richardhawthorn/Build/images/DSC_7647.JPG

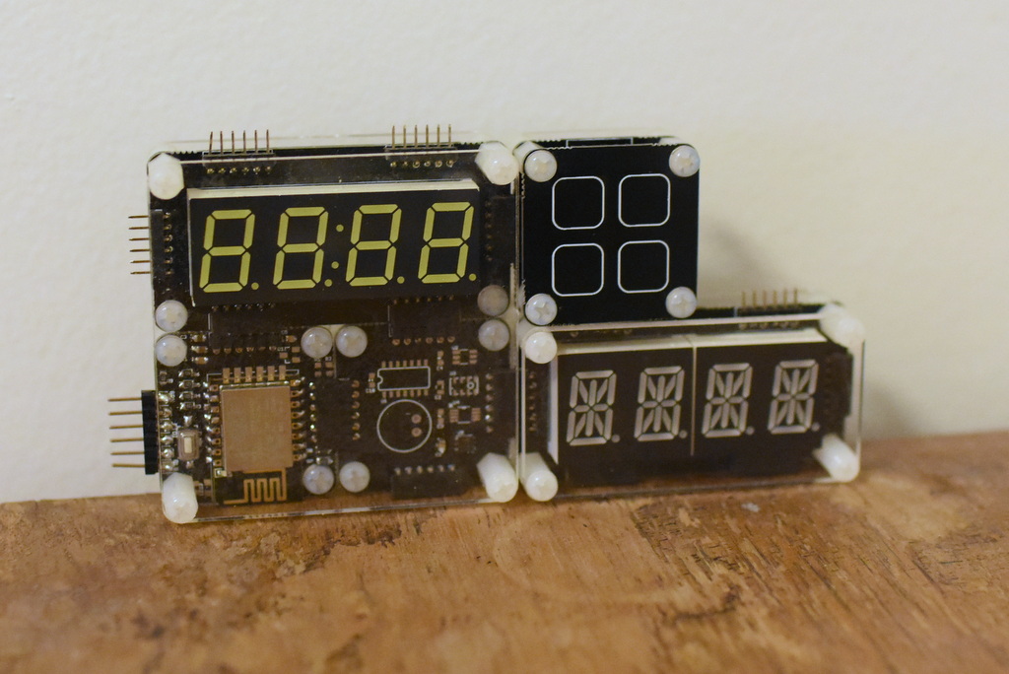
images/DSC_7647.JPG
