richardhawthorn/Build/Boards/7 Segment/images/pcb_back.png

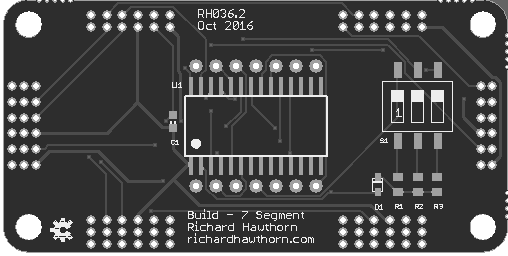
Boards/7 Segment/images/pcb_back.png
