richardhawthorn/Build/Boards/14 Segment/images/DSC_7678.JPG

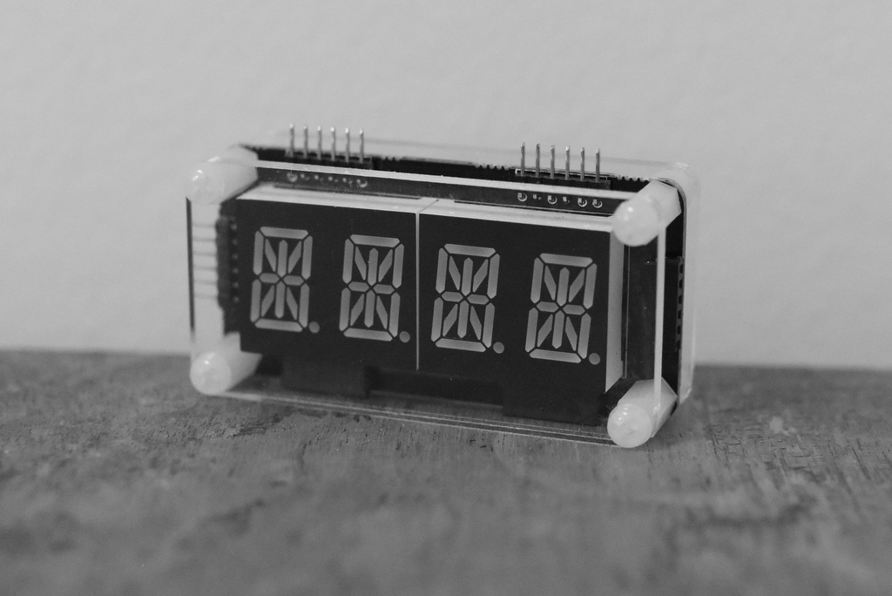
Boards/14 Segment/images/DSC_7678.JPG
