richardhawthorn/Build/Boards/Buttons/images/pcb_back.png

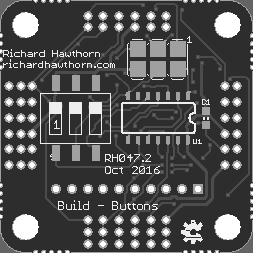
Boards/Buttons/images/pcb_back.png
