richardhawthorn/Build/Boards/Buttons/images/pcb_back_btn.png

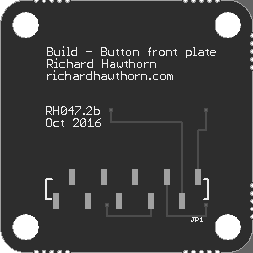
Boards/Buttons/images/pcb_back_btn.png
