richardhawthorn/Build/Boards/Buttons/images/pcb_front.png

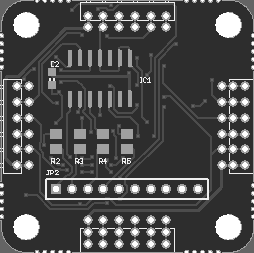
Boards/Buttons/images/pcb_front.png
