richardhawthorn/Build/Boards/Buttons/images/pcb_front_btn.png

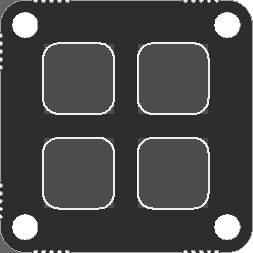
Boards/Buttons/images/pcb_front_btn.png
