richardhawthorn/Build/Boards/Dial/images/pcb_back.png

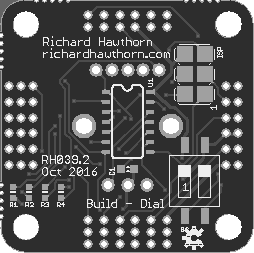
Boards/Dial/images/pcb_back.png
