richardhawthorn/Build/Boards/Dial/images/pcb_front.png

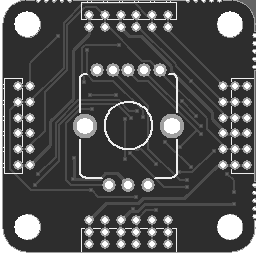
Boards/Dial/images/pcb_front.png
