richardhawthorn/Build/Boards/External Sensors/images/pcb_back.png

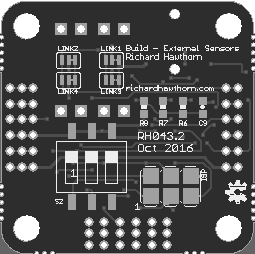
Boards/External Sensors/images/pcb_back.png
