richardhawthorn/Build/Boards/External Sensors/images/pcb_front.png

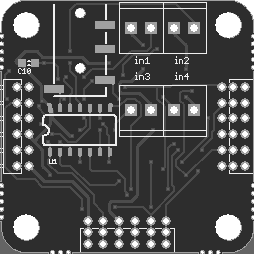
Boards/External Sensors/images/pcb_front.png
