richardhawthorn/Build/Boards/Mini 8x8 Matrix/images/pcb_back.png

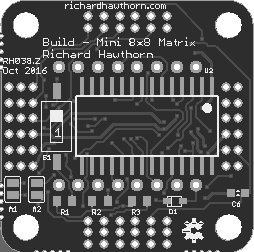
Boards/Mini 8x8 Matrix/images/pcb_back.png
