richardhawthorn/Build/Boards/Mini 8x8 Matrix/images/pcb_front.png

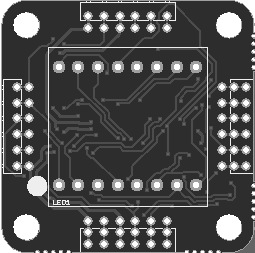
Boards/Mini 8x8 Matrix/images/pcb_front.png
