richardhawthorn/Build/Boards/Neopixel/images/pcb_back.png

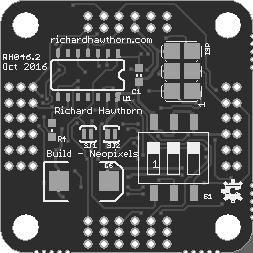
Boards/Neopixel/images/pcb_back.png
