richardhawthorn/Build/Boards/Neopixel/images/pcb_front.png

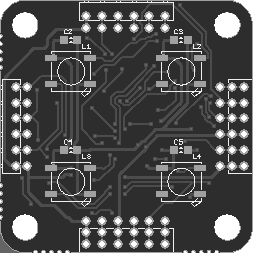
Boards/Neopixel/images/pcb_front.png
