richardhawthorn/Build/Boards/Proto i2c/images/pcb_back.png

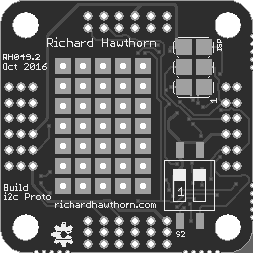
Boards/Proto i2c/images/pcb_back.png
