richardhawthorn/Build/Boards/Proto i2c/images/pcb_front.png

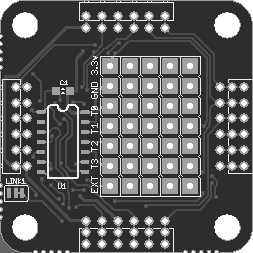
Boards/Proto i2c/images/pcb_front.png
