richardhawthorn/Build/Boards/Proto/images/pcb_back.png

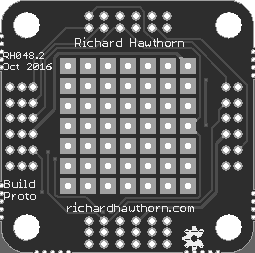
Boards/Proto/images/pcb_back.png
