richardhawthorn/Build/Boards/Proto/images/pcb_front.png

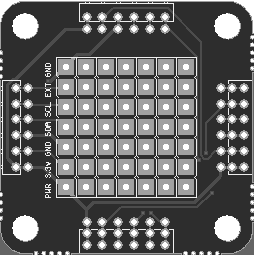
Boards/Proto/images/pcb_front.png
