richardhawthorn/Build/Boards/Relay/images/pcb_back.png

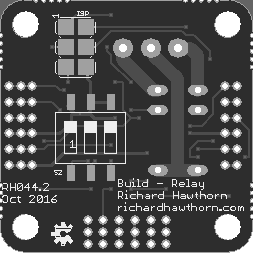
Boards/Relay/images/pcb_back.png
