richardhawthorn/Build/Boards/RF:BLE/images/pcb_back.png

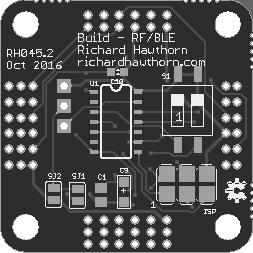
Boards/RF:BLE/images/pcb_back.png
