richardhawthorn/Build/Boards/RF:BLE/images/pcb_front.png

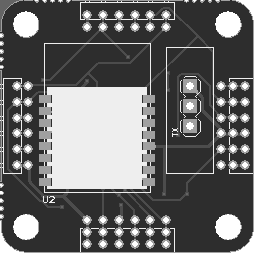
Boards/RF:BLE/images/pcb_front.png
