richardhawthorn/Build/Boards/Sensors/images/pcb_back.png

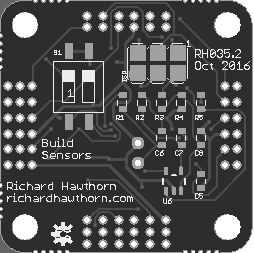
Boards/Sensors/images/pcb_back.png
