richardhawthorn/Build/Boards/Sensors/images/pcb_front.png

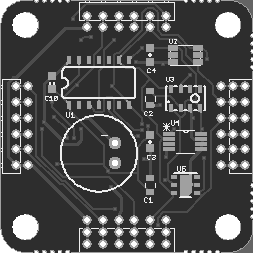
Boards/Sensors/images/pcb_front.png
