richardhawthorn/Build/Boards/Slider/images/pcb_back.png

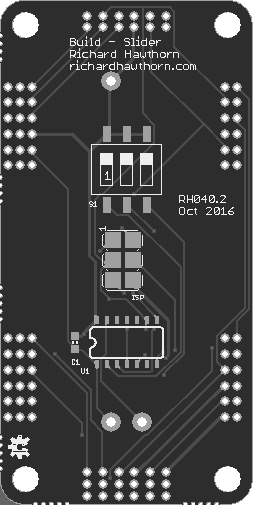
Boards/Slider/images/pcb_back.png
