richardhawthorn/Build/Boards/Wifi Base/images/pcb_back.png

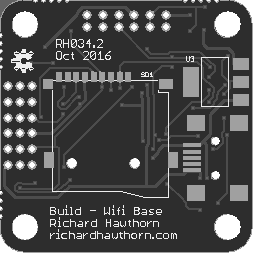
Boards/Wifi Base/images/pcb_back.png
