richardhawthorn/Build/Boards/Wifi Base/images/pcb_front.png

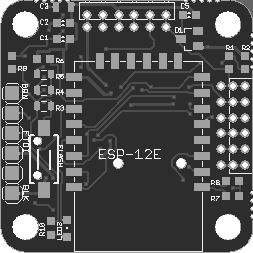
Boards/Wifi Base/images/pcb_front.png
