richardhawthorn/Build/images/DSC_7637.JPG

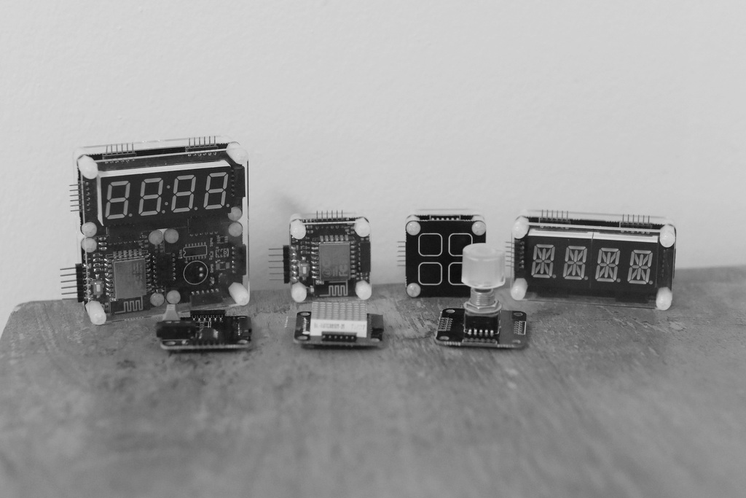
images/DSC_7637.JPG
