richardhawthorn/Build/Boards/RF:BLE/pcb/RH045.2/RH045.2.brd

## EAGLE design Boards/RF:BLE/pcb/RH045.2/RH045.2.brd (2018-01-28)

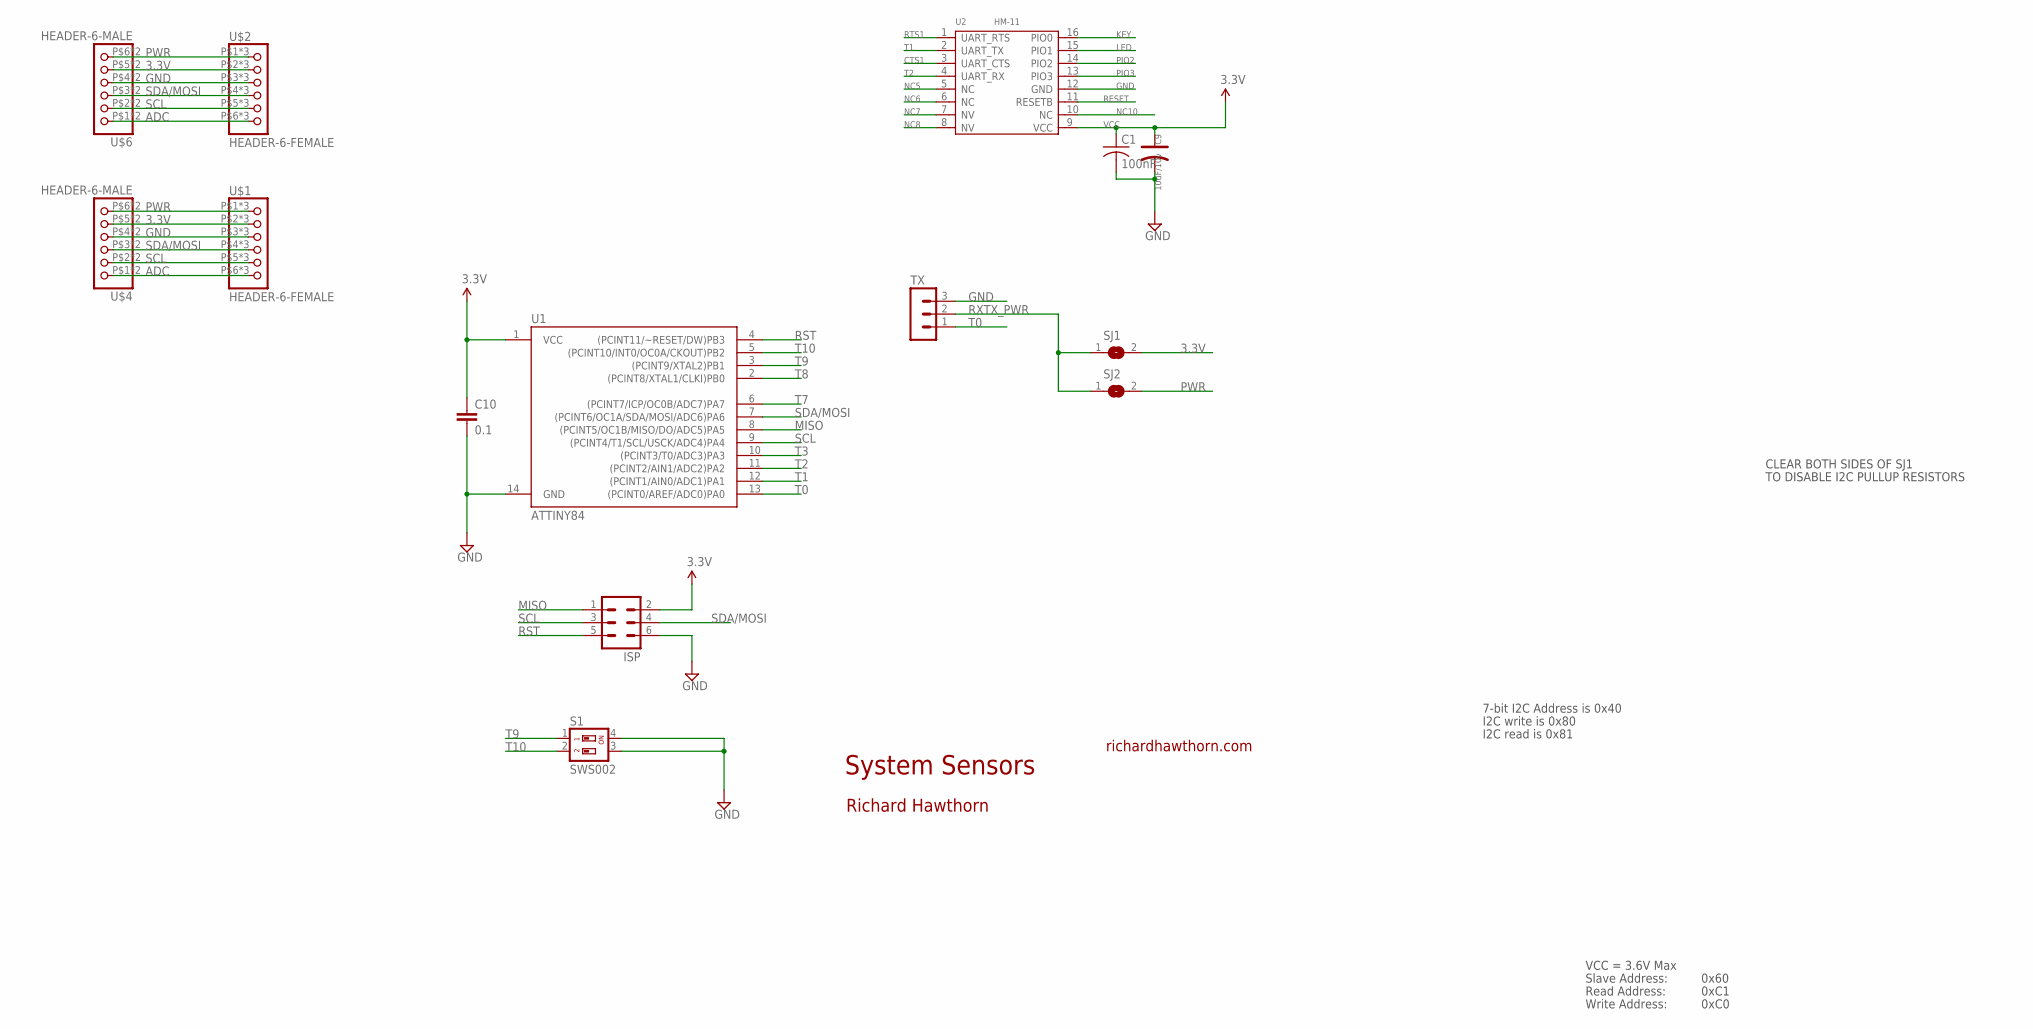
[picture p61: schematic RH045.2.sch]

Parts:
C1: 100nF; C0805
C9: 10uF/10v; AVX-A
C10: 0.1; 0603-CAP
ISP: MA03-2
S1: SWS002; SMS-002
SJ1, SJ2: SJ
TX: MA03-1
U1: ATTINY84; SO14
U2: HM-11; 16P-18.5X13.5X0.8
U$1, U$2: HEADER-6-FEMALE; 2MMHEADER6
U$4, U$6: HEADER-6-MALE; 2MMHEADERPIN6

Connections:
3.3V: C10.1, ISP.2, SJ1.2, U1.1 (VCC), U$1.P$2 (2), U$1.P$10 (2), U$1.P$18 (2), U$2.P$2 (2), U$2.P$10 (2), U$2.P$18 (2), U$4.P$5 (5), U$4.P$13 (5), U$6.P$5 (5), U$6.P$13 (5)
ADC: U$1.P$6 (6), U$1.P$14 (6), U$1.P$22 (6), U$2.P$6 (6), U$2.P$14 (6), U$2.P$22 (6), U$4.P$1 (1), U$4.P$9 (1), U$6.P$1 (1), U$6.P$9 (1)
CTS1: U2.3 (UART_CTS)
GND: C1.2, C9.-, C10.2, ISP.6, S1.3, S1.4, TX.3, U1.14 (GND), U2.12 (GND), U$1.P$3 (3), U$1.P$11 (3), U$1.P$19 (3), U$2.P$3 (3), U$2.P$11 (3), U$2.P$19 (3), U$4.P$4 (4), U$4.P$12 (4), U$6.P$4 (4), U$6.P$12 (4)
KEY: U2.16 (PIO0)
LED: U2.15 (PIO1)
MISO: ISP.1, U1.8 ((PCINT5/OC1B/MISO/DO/ADC5)PA5)
NC5: U2.5 (NC)
NC6: U2.6 (NC)
NC7: U2.7 (NV)
NC8: U2.8 (NV)
NC10: U2.10 (NC)
PIO2: U2.14 (PIO2)
PIO3: U2.13 (PIO3)
PWR: SJ2.2, U$1.P$1 (1), U$1.P$9 (1), U$1.P$17 (1), U$2.P$1 (1), U$2.P$9 (1), U$2.P$17 (1), U$4.P$6 (6), U$4.P$14 (6), U$6.P$6 (6), U$6.P$14 (6)
RESET: U2.11 (RESETB)
RST: ISP.5, U1.4 ((PCINT11/~RESET/DW)PB3)
RTS1: U2.1 (UART_RTS)
RXTX_PWR: SJ1.1, SJ2.1, TX.2
SCL: ISP.3, U1.9 ((PCINT4/T1/SCL/USCK/ADC4)PA4), U$1.P$5 (5), U$1.P$13 (5), U$1.P$21 (5), U$2.P$5 (5), U$2.P$13 (5), U$2.P$21 (5), U$4.P$2 (2), U$4.P$10 (2), U$6.P$2 (2), U$6.P$10 (2)
SDA/MOSI: ISP.4, U1.7 ((PCINT6/OC1A/SDA/MOSI/ADC6)PA6), U$1.P$4 (4), U$1.P$12 (4), U$1.P$20 (4), U$2.P$4 (4), U$2.P$12 (4), U$2.P$20 (4), U$4.P$3 (3), U$4.P$11 (3), U$6.P$3 (3), U$6.P$11 (3)
T0: TX.1, U1.13 ((PCINT0/AREF/ADC0)PA0)
T1: U1.12 ((PCINT1/AIN0/ADC1)PA1), U2.2 (UART_TX)
T2: U1.11 ((PCINT2/AIN1/ADC2)PA2), U2.4 (UART_RX)
T3: U1.10 ((PCINT3/T0/ADC3)PA3)
T7: U1.6 ((PCINT7/ICP/OC0B/ADC7)PA7)
T8: U1.2 ((PCINT8/XTAL1/CLKI)PB0)
T9: S1.1, U1.3 ((PCINT9/XTAL2)PB1)
T10: S1.2, U1.5 ((PCINT10/INT0/OC0A/CKOUT)PB2)
VCC: C1.1, C9.+, U2.9 (VCC)

Notes on the sheet:
System Sensors
richardhawthorn.com
Richard Hawthorn
CLEAR BOTH SIDES OF SJ1
TO DISABLE I2C PULLUP RESISTORS
7-bit I2C Address is 0x40
I2C write is 0x80
I2C read is 0x81
VCC = 3.6V Max
Read Address:
Write Address:
Slave Address:
0x60
0xC1
0xC0

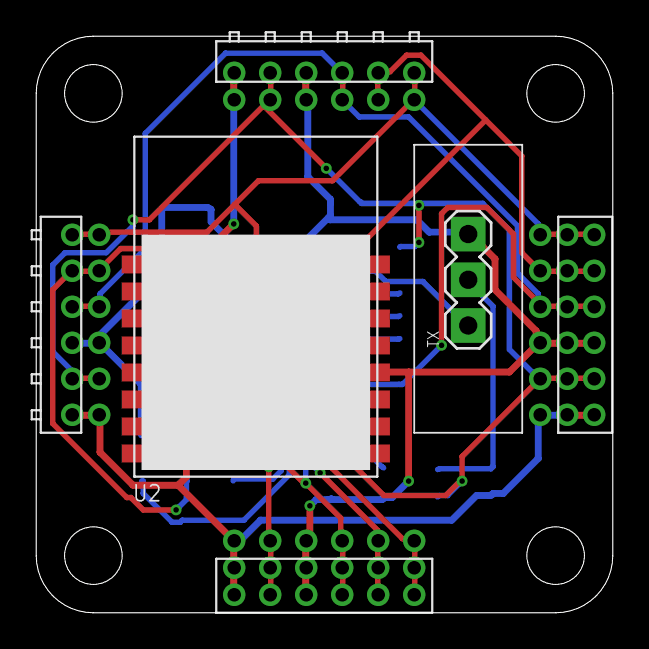
[picture p62: board RH045.2.brd from above]

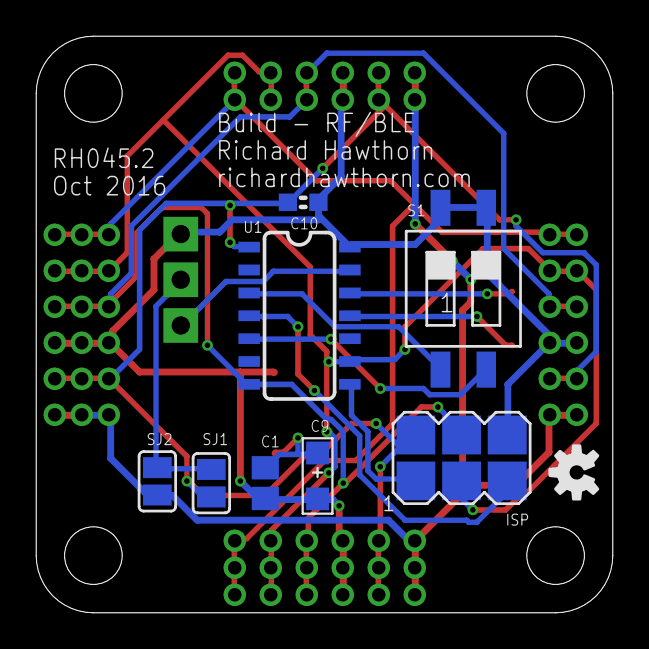
[picture p63: board RH045.2.brd from below]

Board: 2 copper layers, 32.0 x 32.0 mm, 15 parts (9 on the bottom side), 15 nets.

Other parts of the board:
U$3: OSHW-LOGO-S
